545ch4/flippie/code/server/src/flippie_server.h

#ifndef FLIPPIE_SERVER_H
#define FLIPPIE_SERVER_H

#include "flippie.h"
#include "handler/ui_handler.h"
#include "handler/dots_handler.h"
#include "handler/pixel_handler.h"
#include "handler/flippie_handler.h"
#include "handler/not_found_handler.h"
#include <ESP8266WebServer.h>


class FlippieServer {
public:
   FlippieServer(ESP8266WebServer* s);
   ESP8266WebServer* server;
   Flippie* flippie;
};

#endif
