545ch4/flippie/code/server/src/fp2800a.h

#ifndef FP2800A_H
#define FP2800A_H

#define FP2800A_COLUMN_CODE_LINES 5
#define FP2800A_ACTIVE_TIME_IN_USEC 600
#define FP2800A_MAX_COLUMNS 28
#define FP2800A_HGH 1
#define FP2800A_LOW 0

// column index to FP2800A column code (BFP2800A_HGH, B0, A2, AFP2800A_HGH, A0)
// inversed due to the use of NMOS: HIGH => signal to GND
const unsigned int
    FP2800A_COLUMN_CODES[FP2800A_MAX_COLUMNS][FP2800A_COLUMN_CODE_LINES] = {
        {FP2800A_HGH, FP2800A_HGH, FP2800A_HGH, FP2800A_HGH, FP2800A_LOW},
        {FP2800A_HGH, FP2800A_HGH, FP2800A_HGH, FP2800A_LOW, FP2800A_HGH},
        {FP2800A_HGH, FP2800A_HGH, FP2800A_HGH, FP2800A_LOW, FP2800A_LOW},
        {FP2800A_HGH, FP2800A_HGH, FP2800A_LOW, FP2800A_HGH, FP2800A_HGH},
        {FP2800A_HGH, FP2800A_HGH, FP2800A_LOW, FP2800A_HGH, FP2800A_LOW},
        {FP2800A_HGH, FP2800A_HGH, FP2800A_LOW, FP2800A_LOW, FP2800A_HGH},
        {FP2800A_HGH, FP2800A_HGH, FP2800A_LOW, FP2800A_LOW, FP2800A_LOW},
        {FP2800A_HGH, FP2800A_LOW, FP2800A_HGH, FP2800A_HGH, FP2800A_LOW},
        {FP2800A_HGH, FP2800A_LOW, FP2800A_HGH, FP2800A_LOW, FP2800A_HGH},
        {FP2800A_HGH, FP2800A_LOW, FP2800A_HGH, FP2800A_LOW, FP2800A_LOW},
        {FP2800A_HGH, FP2800A_LOW, FP2800A_LOW, FP2800A_HGH, FP2800A_HGH},
        {FP2800A_HGH, FP2800A_LOW, FP2800A_LOW, FP2800A_HGH, FP2800A_LOW},
        {FP2800A_HGH, FP2800A_LOW, FP2800A_LOW, FP2800A_LOW, FP2800A_HGH},
        {FP2800A_HGH, FP2800A_LOW, FP2800A_LOW, FP2800A_LOW, FP2800A_LOW},
        {FP2800A_LOW, FP2800A_HGH, FP2800A_HGH, FP2800A_HGH, FP2800A_LOW},
        {FP2800A_LOW, FP2800A_HGH, FP2800A_HGH, FP2800A_LOW, FP2800A_HGH},
        {FP2800A_LOW, FP2800A_HGH, FP2800A_HGH, FP2800A_LOW, FP2800A_LOW},
        {FP2800A_LOW, FP2800A_HGH, FP2800A_LOW, FP2800A_HGH, FP2800A_HGH},
        {FP2800A_LOW, FP2800A_HGH, FP2800A_LOW, FP2800A_HGH, FP2800A_LOW},
        {FP2800A_LOW, FP2800A_HGH, FP2800A_LOW, FP2800A_LOW, FP2800A_HGH},
        {FP2800A_LOW, FP2800A_HGH, FP2800A_LOW, FP2800A_LOW, FP2800A_LOW},
        {FP2800A_LOW, FP2800A_LOW, FP2800A_HGH, FP2800A_HGH, FP2800A_LOW},
        {FP2800A_LOW, FP2800A_LOW, FP2800A_HGH, FP2800A_LOW, FP2800A_HGH},
        {FP2800A_LOW, FP2800A_LOW, FP2800A_HGH, FP2800A_LOW, FP2800A_LOW},
        {FP2800A_LOW, FP2800A_LOW, FP2800A_LOW, FP2800A_HGH, FP2800A_HGH},
        {FP2800A_LOW, FP2800A_LOW, FP2800A_LOW, FP2800A_HGH, FP2800A_LOW},
        {FP2800A_LOW, FP2800A_LOW, FP2800A_LOW, FP2800A_LOW, FP2800A_HGH},
        {FP2800A_LOW, FP2800A_LOW, FP2800A_LOW, FP2800A_LOW, FP2800A_LOW}};
#endif
