545ch4/flippie/code/server/src/handler/dots_handler.h

#ifndef DOTS_HANDLER_H
#define DOTS_HANDLER_H
#include "../base64.h"
#include "../flippie.h"
#include "abstract_handler.h"
#include <ESP8266WebServer.h>

class DotsHandler : public AbstractHandler {
public:
  DotsHandler(Flippie* flippie);
  bool canHandle(HTTPMethod method, String uri) override;
  bool handle(ESP8266WebServer& server, HTTPMethod method, String uri) override;
protected:
  Flippie* flippie;
  Base64 b64;
};

#endif
